LukinaChen/TECHIN-514--Hardware-Software--Final-Project/Display Enclosure/PCB Source_v3.step

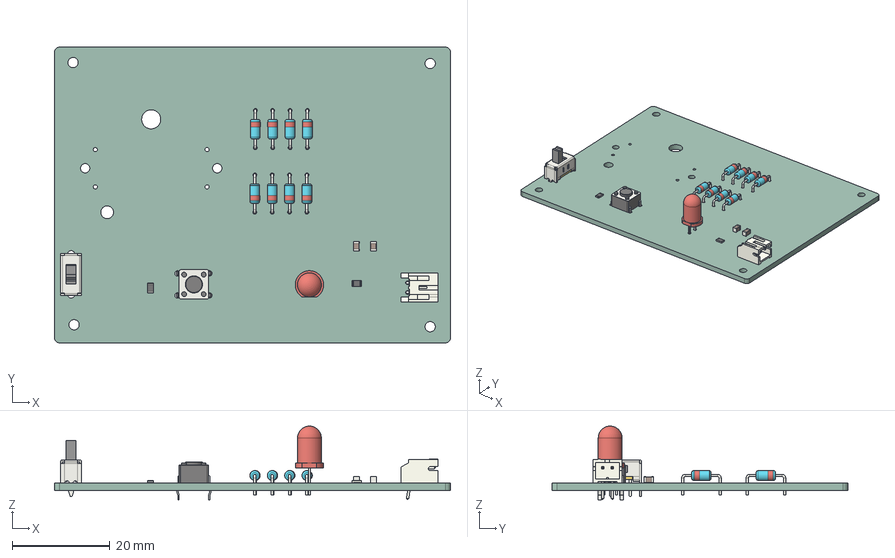
[picture p41: CAD file, 2026-02-22]
Display Enclosure/PCB Source_v3.step
81.0 x 60.5 x 15.1 mm
C_0805_2012Metric x 2
R_0805_2012Metric x 2
D_DO-35_SOD27_P7.62mm_Horizontal x 8
JST_PH_S2B-PH-K_1x02_P2.00mm_Horizontal
LED_D5.0mm
SW_Slide_SPDT_Straight_CK_OS102011MS2Q
SW_PUSH_6mm
SnoreSense_Display_PCB_v1_PCB
