LukinaChen/TECHIN-514--Hardware-Software--Final-Project/Display Enclosure/Enclosure-Display_step.step

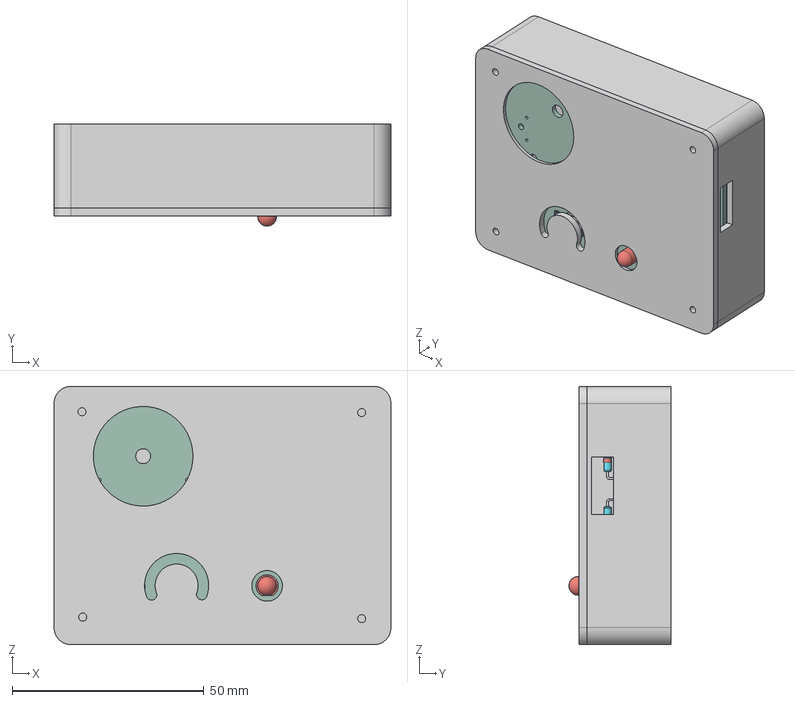
[picture p42: CAD file, 2026-02-22]
Display Enclosure/Enclosure-Display_step.step
88.0 x 26.7 x 67.5 mm
